Beo-Coder/muek-TGLBoard/src/dinoGame.h

//
// Created by leo on 25.04.24.
//

#ifndef MUEK_ARGB_MATRIX_BOARD_DINOGAME_H
#define MUEK_ARGB_MATRIX_BOARD_DINOGAME_H

#include "Arduino.h"
#include "pioMatrixOutput.h"
#include "color.h"
#include "display_program.h"
#include "BeoCommon.h"




// Enemy section
#define MAX_ENEMIES 2

#define ENEMY_BIRD 0
#define ENEMY_WORM 1
#define ENEMY_ENEMY 2

#define ENEMY_SIZE_1 0
#define ENEMY_SIZE_2 1

#define ENEMY_TYPES 6


static int8_t enemyHeights[ENEMY_TYPES][4] = {{0, 2, ENEMY_ENEMY, ENEMY_SIZE_2},
                                              {0, 4, ENEMY_WORM,  ENEMY_SIZE_1},
                                              {3, 2, ENEMY_BIRD,  ENEMY_SIZE_1},
                                              {6, 1, ENEMY_BIRD,  ENEMY_SIZE_1},
                                              {5, 1, ENEMY_BIRD,  ENEMY_SIZE_1},
                                              {4, 1, ENEMY_BIRD,  ENEMY_SIZE_1}
}; // 0: height; 1: probability; 2: enemySkin; 3: enemySizeIndex;

static int8_t enemySize[3][2] = {
        {3, 2},
        {2, 3},
};
// Enemy section END

// Player section
#define PLAYER_POS_X 2
#define PLAYER_POS_Y 0

#define PLAYER_SIZE_X 2
#define PLAYER_SIZE_Y 4

#define PLAYER_JUMP_HEIGHT 3
#define PLAYER_JUMP_LENGTH 9
#define PLAYER_DUCK_HEIGHT (-1)
// Player section END

// Level section
#define LEVELS 12

static uint32_t levels[LEVELS][3] = {
        {0,    100, 1},
        {100,  100, 2},
        {500,  95,  2},
        {1000, 90,  2},
        {1300, 85,  2},
        {1600, 80,  2},
        {1900, 75,  2},
        {2100, 70,  2},
        {2300, 65,  2},
        {2500, 60,  2},
        {2700, 55,  2},
        {3000, 50,  2}}; // score, speed, enemies

// Level section END




/*
static Color colorDarkRed;
static Color colorRed;
static Color colorGrey;
static Color colorGreen;
static Color colorBlank;
 */



static Color *entityColorBlank = &colorBlank;

static Color *playerColor1 = &colorGreen;
static Color *playerColor2 = &colorWhite;


static Color **playerSkin[4][4][2] = {
        {
                {&playerColor1, &playerColor1},
                {&playerColor1, &playerColor2},
                {&playerColor1,     &playerColor1},
                {&playerColor1,     &entityColorBlank},
        },
        {
                {&playerColor1, &playerColor1},
                {&playerColor1, &playerColor2},
                {&playerColor1,     &playerColor1},
                {&entityColorBlank, &playerColor1},
        },
        {
                {&playerColor1, &playerColor1},
                {&playerColor1, &playerColor2},
                {&playerColor1,     &entityColorBlank},
        },
        {
                {&playerColor1, &playerColor1},
                {&playerColor1, &playerColor2},
                {&entityColorBlank, &playerColor1},
        }
};

/*
static Color colorEnemyDarkRed(3,0,0);
static Color colorEnemyOrange;
static Color colorEnemyBlue;
 */

static Color *colorCollision = new Color(3,0,0);


static Color *enemyColor1 = &colorPurple;
static Color *enemyColor2 = &colorRed;
static Color *enemyColor3 = new Color(2,1,0);
static Color *enemyColor4 = &colorBlue;



static Color **enemySkin[10][4][4] = {
        {
                {&entityColorBlank, &enemyColor1,      &entityColorBlank},
                {&enemyColor2, &enemyColor1,      &enemyColor1},
        },
        {
                {&entityColorBlank, &entityColorBlank, &entityColorBlank},
                {&enemyColor2, &enemyColor1,      &enemyColor1},
        },
        {
                {&entityColorBlank, &enemyColor3,      &entityColorBlank},
                {&enemyColor3, &entityColorBlank, &enemyColor3},
        },
        {
                {&entityColorBlank, &entityColorBlank, &entityColorBlank},
                {&enemyColor3, &enemyColor3,      &enemyColor3},
        },
        {
                {&enemyColor4,      &enemyColor4},
                {&enemyColor2, &enemyColor4},
                {&enemyColor4,      &entityColorBlank},
        },
        {

                {&enemyColor4,      &enemyColor4},
                {&enemyColor2, &enemyColor4},
                {&entityColorBlank, &enemyColor4},

        }
};

namespace details_dino_game {
    class Entity {
    public:
        int8_t posX;
        int8_t posY;
        int8_t sizeX;
        int8_t sizeY;

        uint8_t skinIndex = 0;


        Entity(int8_t startPosX, int8_t startPosY, int8_t sizeX, int8_t sizeY);
        Entity();


        virtual void animate(Color (*display)[MATRIX_HEIGHT][MATRIX_LENGTH]) = 0;


    };

    class Enemy : public Entity {
    public:

        Enemy(int8_t startPosX, int8_t startPosY, int8_t sizeX, int8_t sizeY);
        Enemy();

        uint8_t enemyType;
        bool alive;




        void animate(Color (*display)[MATRIX_HEIGHT][MATRIX_LENGTH]) override;
        void move();



    };


    class Player : public Entity {
        int32_t lastJump;


    public:

        Player(int8_t startPosX, int8_t startPosY, int8_t sizeX, int8_t sizeY);

        void jump();

        void duck(bool pressed);

        void checkJumped();

        void animate(Color (*display)[MATRIX_HEIGHT][MATRIX_LENGTH]) override;

        bool checkAndMarkCollision(const Enemy &entity, Color (*display)[MATRIX_HEIGHT][MATRIX_LENGTH]);

    };
}

class DinoGame : public display_program {


    details_dino_game::Enemy *enemies[MAX_ENEMIES];
    uint8_t numberEnemies;
    details_dino_game::Player *player;

    bool dead = false;

    void animateFrame();

    void moveEntities();

    void createNewEnemy(uint8_t index);

    void checkScore();


public:
    uint32_t score;

    explicit DinoGame(MatrixOutput *ledMatrix, Color (*frame)[MATRIX_HEIGHT][MATRIX_LENGTH]);

    void button1ISR(bool data) override;

    void button2ISR(bool data) override;

    void refresh() override;

    void restart() override;


};


#endif //MUEK_ARGB_MATRIX_BOARD_DINOGAME_H
