Beo-Coder/muek-TGLBoard/src/beo_common.cpp

//
// © 2024 Leonhard Baschang
//

#include "beo_common.h"
#include <hardware/structs/rosc.h>
#include <hardware/timer.h>

int beo::randomInt(int min, int max){
    int range = (max-min);
    uint32_t randomNumber;
    for(int i=0; i<4*8;i++){
        randomNumber = (randomNumber << 1) | rosc_hw->randombit;
    }

    return int(randomNumber % range) + min;
}

unsigned long beo::millis() {
    return time_us_64() / 1000;

}
