Beo-Coder/muek-TGLBoard/src/beo_common.h

//
// © 2024 Leonhard Baschang
//

#ifndef TGL_BOARD_BEO_COMMON_H
#define TGL_BOARD_BEO_COMMON_H

#define absolute(x) ((x)>0?(x):-(x))

namespace beo{
    int randomInt(int min, int max);

    unsigned long millis();


}


#endif //TGL_BOARD_BEO_COMMON_H
