Beo-Coder/muek-TGLBoard/src/TetrisGame/tetris.h

//
// Created by thijs on 08.05.24.
//

#ifndef TETRIS_TETRIS_H
#define TETRIS_TETRIS_H

class TextController;
class Block;
class FlashController;

#include "display_program.h"
#include <string>




#define SCROLL_SPEED 400
#define SCORE_TEXT_SCROLL_SPEED 200
#define LOSS_DELAY 6000
#define START_X 2
#define START_Y 0

#define LOSS_Y 2

#define TETRIS_FLASH_ACCESS_KEY 2
#define TETRIS_FLASH_SIZE 4

class Tetris : public DisplayProgram{
public:
    // display program requirements:
    void refresh() override;
    void restart() override;

    void button1ISR(bool data) override; // select
    void button2ISR(bool data) override; // mode


    //explicit Tetris(MatrixOutput* matrix);
    explicit Tetris(MatrixOutput *ledMatrix, Color (*frame)[MATRIX_HEIGHT][MATRIX_LENGTH], TextController *scrollController, FlashController *flashController);

    void reset();
    void loop();

    void moveLeft();
    void moveRight();
    void rotate();


private:
    TextController *textController;
    FlashController *flashController;

    static uint32_t getHighScore();
    void storeHighScore();
    void checkHighScore();
    void lossTick();

    bool rotated;
    bool button1Cache;
    bool button2Cache;
    std::string stringBuffer;

    bool loss;
    uint8_t lossState;
    unsigned int score;

    unsigned int tickCnt;

    Block* flyingBlock;
    volatile int blockX;
    volatile int blockY;
    volatile bool scheduleRotation;


    bool map[MATRIX_HEIGHT][MATRIX_LENGTH] = {};
    Color* colorMap[MATRIX_HEIGHT][MATRIX_LENGTH] = {};

    void copyMapIntoDisplay();
    void mergeBlockIntoDisplay();
    void mergeOverlayIntoDisplay();
    void mergeBlockIntoMap();

    void generateNewBlock();

    bool detectCollision();
    void detectAndDeleteRow();
    void detectLoss();
    static uint32_t genRandomNumber(int max);

    unsigned long prevMillis;
    unsigned int tickSpeed = SCROLL_SPEED;
    unsigned int frameSpeed = 17; // about 60fps

    unsigned long prevScrollMillis;

    void tick();
    void graphicTick();
    void handleScheduledActions();


};


#endif //TETRIS_TETRIS_H
