Beo-Coder/muek-TGLBoard/src/color.h

//
// Created by leo on 03.04.24.
//

#ifndef MUEK_ARGB_MATRIX_BOARD_COLOR_H
#define MUEK_ARGB_MATRIX_BOARD_COLOR_H

#include "Arduino.h"

#define MAX_COLOR_VALUE 255
#define MIN_COLOR_VALUE 0

#define NORMAL_BRIGHTNESS 1

#define MIN_BRIGHTNESS 1
#define MAX_BRIGHTNESS 255


class Color {



    float brightness;


    static float checkAndReturnValid(float value);

public:

    float blue;
    float red;
    float green;

    bool equals(Color* reference); // this can not compare colors, just if the color is sourced from the same object

    void set(Color* reference);
    void add(Color* addition);
    void multiply(float factor);
    void average(Color* addition);

    void setRed(float value);
    void setGreen(float value);
    void setBlue(float value);

    float getRed(bool raw=false);
    float getGreen(bool raw=false);
    float getBlue(bool raw=false);

    void setRGB(uint8_t colorNumber, float value); // 0: red; 1: green; 2: blue
    float getRGB(uint8_t colorNumber, bool raw=false); // 0: red; 1: green; 2: blue

    void setBrightness(float value);
    float getBrightness();



    Color(float red, float green, float blue);
    Color();

    uint32_t calc();
};

// Clear "color"
static Color colorBlank(0,0,0);

// Some static colors
static Color colorRed(NORMAL_BRIGHTNESS,0,0);
static Color colorGreen(0,NORMAL_BRIGHTNESS,0);
static Color colorBlue(0,0,NORMAL_BRIGHTNESS);

static Color colorWhite(NORMAL_BRIGHTNESS,NORMAL_BRIGHTNESS,NORMAL_BRIGHTNESS);
static Color colorYellow(NORMAL_BRIGHTNESS,NORMAL_BRIGHTNESS,0);
static Color colorCyan(0,NORMAL_BRIGHTNESS,NORMAL_BRIGHTNESS);
static Color colorPurple(NORMAL_BRIGHTNESS,0,NORMAL_BRIGHTNESS);

#define NUMBER_NORMAL_COLORS 7
static Color *allColors[NUMBER_NORMAL_COLORS] = {&colorRed, &colorBlue, &colorGreen, &colorWhite, &colorYellow, &colorCyan, &colorPurple};


#endif //MUEK_ARGB_MATRIX_BOARD_COLOR_H
